mbuesch/cnc-control/schematics/cnc-control.sch

## KiCad design schematics/cnc-control.sch (2011-06-05)

Schematic: cnc-control.sch

Parts:
C1: 100u
C2: 47p
C3, C4, C5, C6, C7: 100n
D1: USB link
D2, D3, D4, D5, D6, D7, D8, D9, D10, D11, D12, D13, D14: LED
J1: USB
K1: DEBUG
LCD1: HD44780
P1: SCK_SELECT
P2: ISP
R1: 1k
R2, R6, R7, R8, R23: 10k
R3, R4: 33
R5, R10, R11, R12, R13, R14, R15, R16, R17, R18, R19, R20, R21, R22: 470
R9: 100
RV1: 50k
RV2: Feed override (47k)
SW1: X_SEL
SW2: Y_SEL
SW3: Z_SEL
SW4: A_SEL
SW5: SPINDLE
SW6: TWOHAND
SW7: JOG_POSITIVE
SW8: RAPID
SW9: JOG_NEGATIVE
SW10: JOG_INCREMENTAL
SW11: SOFTKEY_0
SW12: ON/OFF_KEY
SW13: SOFTKEY_1
SW14: Jogwheel
SW15: BOOT_RESCUE
U1: 74HCT4094 / 1
U2: 74HCT4094 / 0
U3: PDIUSBD12
U4: ATMEGA32
U5: ATMEGA8
X1: 16MHz OSC
X2: 6MHz OSC

Notes on the sheet:
Jumper on 1-3 = Program AtMega8.
Jumper on 2-4 = Program AtMega32.
Jumper on 1-2 = Normal op. No prog.
In-system-programming SCK select:
Main processor
Button coprocessor
