mbuesch/cnc-control/schematics/pdiusb-adapter.sch

## KiCad design schematics/pdiusb-adapter.sch (2011-06-05)

Schematic: pdiusb-adapter.sch

Parts:
P1, P2: CONN_14
U1: PDIUSBD12
