mbuesch/cnc-control/driver/setup_driver.py

from setuptools import setup

setup(
	name		= "cnccontrol-driver",
	description	= "CNC-Control device driver",
	author		= "Michael Büsch",
	author_email	= "m@bues.ch",
	py_modules	= [ "cnccontrol_driver", ],
)
