mbuesch/cnc-control/firmware/cpu-firmware/lcd.c

/*
 *   4-bit HD44780 LCD support
 *
 *   Copyright (C) 2007-2016 Michael Buesch <m@bues.ch>
 *
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
 *   This program is distributed in the hope that it will be useful,
 *   but WITHOUT ANY WARRANTY; without even the implied warranty of
 *   MERCHANTABILITY or FITNESS FOR A PARTICULAR PURPOSE.  See the
 *   GNU General Public License for more details.
 */

#include "lcd.h"

#include <avr/io.h>
#include <util/delay.h>

#include <string.h>
#include <stdio.h>


#define LCD_NR_CHARS		(LCD_NR_LINES * LCD_NR_COLUMNS)
#define LCD_BUFFER_SIZE		LCD_NR_CHARS

static uint8_t lcd_buffer[LCD_BUFFER_SIZE];
uint8_t lcd_cursor_pos;


/** lcd_enable_pulse - Send an E-pulse */
static void lcd_enable_pulse(void)
{
	LCD_PORT = (uint8_t)(LCD_PORT | LCD_PIN_E);
	__asm__ __volatile__("nop\n\t"
			     "nop\n\t"
			     : : : "memory");
	LCD_PORT = (uint8_t)(LCD_PORT & ~LCD_PIN_E);
}

/** lcd_write - Write one byte to the LCD. */
static void lcd_write(uint8_t data)
{
	LCD_PORT = (uint8_t)((LCD_PORT & ~(0xF << LCD_DATA_SHIFT)) |
			     (((data & 0xF0) >> 4) << LCD_DATA_SHIFT));
	lcd_enable_pulse();
	LCD_PORT = (uint8_t)((LCD_PORT & ~(0xF << LCD_DATA_SHIFT)) |
			     ((data & 0x0F) << LCD_DATA_SHIFT));
	lcd_enable_pulse();
	_delay_us(50);
}

/** lcd_data - Send data to the LCD. */
static void lcd_data(uint8_t data)
{
	LCD_PORT = (uint8_t)(LCD_PORT | LCD_PIN_RS);
	lcd_write(data);
}

/** lcd_command - Send command to the LCD. */
static void lcd_command(uint8_t command)
{
	LCD_PORT = (uint8_t)(LCD_PORT & ~LCD_PIN_RS);
	lcd_write(command);
}

/** lcd_cmd_clear - Clear LCD and return cursor to home position. */
static void lcd_cmd_clear(void)
{
	lcd_command(0x01);
	_delay_ms(2);
}

/** lcd_cmd_home - Move cursor to home position. */
static void lcd_cmd_home(void)
{
	lcd_command(0x02);
	_delay_ms(2);
}

/** lcd_cmd_entrymode - Set entry mode.
 * @cursor_inc: 1 = increment cursor, 0 = decrement cursor.
 * @display_shift: 1 = shift display, 0 = don't shift display.
 */
static void lcd_cmd_entrymode(uint8_t cursor_inc,
			      uint8_t display_shift)
{
	lcd_command((uint8_t)(0x04u |
			      (cursor_inc ? 0x02u : 0x00u) |
			      (display_shift ? 0x01u : 0x00u)));
}

/** lcd_cmd_dispctl - Display control.
 * @display_on: 1 = turn display on, 0 = turn display off.
 * @cursor_on: 1 = turn cursor on, 0 = turn cursor off.
 * @cursor_blink: 1 = blink cursor, 0 = don't blink cursor.
 */
void lcd_cmd_dispctl(uint8_t display_on,
		     uint8_t cursor_on,
		     uint8_t cursor_blink)
{
	lcd_command((uint8_t)(0x08u |
			      (display_on ? 0x04u : 0x00u) |
			      (cursor_on ? 0x02u : 0x00u) |
			      (cursor_blink ? 0x01u : 0x00u)));
}

/** lcd_cmd_shiftctl - Display shift control.
 * @shift_display: 1 = move display, 0 = move cursor.
 * @shift_right: 1 = right direction, 0 = left direction.
 */
static void lcd_cmd_shiftctl(uint8_t shift_display,
			     uint8_t shift_right)
{
	lcd_command((uint8_t)(0x10u |
			      (shift_display ? 0x08u : 0x00u) |
			      (shift_right ? 0x04u : 0x00u)));
}

/** lcd_cmd_funcset - Set basic display function.
 * @eight_bit: 1 = 8bit mode, 0 = 4bit mode.
 * @two_lines: 1 = two rows, 0 = one row.
 * @font_5x10: 1 = 5x10 font, 0 = 5x8 font.
 */
static void lcd_cmd_funcset(uint8_t eight_bit,
			    uint8_t two_lines,
			    uint8_t font_5x10)
{
	lcd_command((uint8_t)(0x20u |
			      (eight_bit ? 0x10u : 0x00u) |
			      (two_lines ? 0x08u : 0x00u) |
			      (font_5x10 ? 0x04u : 0x00u)));
}

/** lcd_cmd_cgram_addr_set - Move CGRAM address pointer.
 * @address: The address to move to.
 */
static void lcd_cmd_cgram_addr_set(uint8_t address)
{
	lcd_command((uint8_t)(0x40u | (address & 0x3Fu)));
}

/** lcd_cmd_cursor - Move cursor (DDRAM address).
 * @line: Line number. 0 - 1.
 * @column: Column number. 0 - 15.
 */
void lcd_cmd_cursor(uint8_t line, uint8_t column)
{
	lcd_command((uint8_t)(0x80u |
			      ((line & (LCD_NR_LINES - 1u)) << 6u) |
			      (column & (LCD_NR_COLUMNS - 1u))));
}

/** lcd_clear_buffer - Clear the software buffer. */
void lcd_clear_buffer(void)
{
	memset(lcd_buffer, ' ', LCD_BUFFER_SIZE);
	lcd_cursor_pos = 0;
}

/** lcd_commit - Write the software buffer to the display. */
void lcd_commit(void)
{
	uint8_t line, col;
	const uint8_t *buf = lcd_buffer;

	for (line = 0; line < LCD_NR_LINES; line++) {
		lcd_cmd_cursor(line, 0);
		for (col = 0; col < LCD_NR_COLUMNS; col++)
			lcd_data(*buf++);
	}
	lcd_cmd_cursor(lcd_getline(), lcd_getcolumn());
}

/** lcd_put_char - Put one character into software buffer. */
void lcd_put_char(char c)
{
	uint8_t line, column;

	if (c == '\r') {
		lcd_cursor(lcd_getline(), 0);
	} else if (c == '\n') {
		line = (uint8_t)(lcd_getline() + 1u);
		lcd_cursor(line & (LCD_NR_LINES - 1u), 0);
	} else {
		lcd_buffer[lcd_cursor_pos] = (uint8_t)c;
		column = (lcd_getcolumn() + 1u) & (LCD_NR_COLUMNS - 1u);
		lcd_cursor(lcd_getline(), column);
	}
}

static int lcd_stream_putchar(char c, FILE *unused)
{
	lcd_put_char(c);
	return 0;
}

static FILE lcd_fstream = FDEV_SETUP_STREAM(lcd_stream_putchar, NULL,
					    _FDEV_SETUP_WRITE);

void _lcd_printf(const char PROGPTR *fmt, ...)
{
	va_list args;

	va_start(args, fmt);
	vfprintf_P(&lcd_fstream, fmt, args);
	va_end(args);
}

void lcd_put_pstr(const char PROGPTR *str)
{
	uint8_t c;

	for ( ; ; str++) {
		c = pgm_read_byte(str);
		if (c == '\0')
			break;
		lcd_put_char((char)c);
	}
}

/** lcd_upload_char - Upload a user defined character to CGRAM.
 * @char_code: The character code to use.
 * @char_tab: The character bitmap. The bitmap has got one byte
 *	per character pixel row. The upper 3 bits of each byte
 *	are unused. For 5x10 char-pixel displays, the char_tab
 *	is 10 bytes long. For 5x8 char-pixel displays, it's 8 bytes.
 */
void lcd_upload_char(uint8_t char_code,
		     const uint8_t PROGPTR *char_tab)
{
	uint8_t i, c, address;

	address = (uint8_t)(char_code << (LCD_FONT_5x10 ? 4u : 3u));
	for (i = 0; i < (LCD_FONT_5x10 ? 10u : 8u); i++) {
		lcd_cmd_cgram_addr_set(address);
		c = pgm_read_byte(char_tab);
		lcd_data(c);
		address++;
		char_tab++;
	}
	lcd_cmd_cursor(lcd_getline(), lcd_getcolumn());
}

/** lcd_init - Initialize the LCD. */
void lcd_init(void)
{
	uint8_t i;

	LCD_DDR = (uint8_t)(LCD_DDR | (0xFu << LCD_DATA_SHIFT) |
				      LCD_PIN_E | LCD_PIN_RS);

	/* Force it into 8-bit mode first */
	LCD_PORT = (uint8_t)(LCD_PORT & ~(LCD_PIN_E | LCD_PIN_RS |
					  (0xFu << LCD_DATA_SHIFT)));
	LCD_PORT = (uint8_t)(LCD_PORT | (0x03u << LCD_DATA_SHIFT));
	long_delay_ms(200);
	for (i = 3; i; i--) {
		lcd_enable_pulse();
		_delay_ms(5);
	}
	/* We're in a known state. Enable 4-bit mode. */
	LCD_PORT = (uint8_t)((LCD_PORT & ~(0xFu << LCD_DATA_SHIFT)) |
			     (0x02u << LCD_DATA_SHIFT));
	lcd_enable_pulse();
	_delay_ms(10);

	lcd_cmd_funcset(0,
			(LCD_NR_LINES > 1) ? 1 : 0,
			LCD_FONT_5x10 ? 1 : 0);
	lcd_cmd_dispctl(0, 0, 0);
	lcd_cmd_clear();
	lcd_cmd_entrymode(1, 0);
	lcd_cmd_shiftctl(0, 0);
	lcd_cmd_dispctl(1, 0, 0);
	lcd_cmd_home();

	lcd_cursor_pos = 0;
	lcd_clear_buffer();
	lcd_commit();
}
